ali1234/avr-teletext/globals.h

/*
 * Global register variables.
 */

#ifdef __ASSEMBLER__

//#  define oline_counter  r3

#else  /* !ASSEMBLER */

#include <stdint.h>

//register uint8_t line_counter asm("r3");

#endif /* ASSEMBLER */



#define NBUFFERS 22
